SCU-Maker-Org/Mobile_Industrial_Foreign_Object_Detection_Robot/Vehicle_Code/Tracked_407/Core/Src/PID.c

//
// Created by s on 2026/9/23.
//

#include "PID.h"

/**
 * @brief 初始化PID位置控制器（带限幅参数）
 * @param[out] pid PID控制器结构体指针
 * @param[in] Kp 比例系数
 * @param[in] Ki 积分系数
 * @param[in] Kd 微分系数
 * @param[in] integral_limit 积分限幅值
 * @param[in] output_limit 输出限幅值
 */
void PID_Position_Controller_Init(PID_Position_Controller *pid,
                                  float Kp, float Ki, float Kd,
                                  float integral_limit,
                                  float output_limit) {
    pid->Kp = Kp;
    pid->Ki = Ki;
    pid->Kd = Kd;
    pid->error      = 0.0;
    pid->last_error = 0.0;
    pid->prev_error = 0.0;
    pid->differ_error = 0.0;
    pid->sum_error = 0.0;
    pid->output     = 0.0;
    pid->integral_limit = integral_limit;
    pid->output_limit   = output_limit;
}

/**
 * @brief 位置环误差累计限幅内联函数
 */
inline float Limit_Position(float cal_value, float limit_value) {
    if (cal_value > limit_value)    return limit_value;
    if (cal_value < -limit_value)   return -limit_value;

    return cal_value;
}

/**
 * @brief PID位置环更新
 * @param[out] pid PID控制器结构体指针
 * @param[in] target_val 目标值
 * @param[in] current_val 当前值
 * @return output 输出
 */
float PID_Position_Controller_Update(PID_Position_Controller *pid,
                                     float target_val,
                                     float current_val) {
    pid->error = target_val - current_val;
    pid->sum_error += pid->error;
    pid->differ_error = pid->error - pid->last_error;

    pid->output = pid->Kp * pid->error +
                  Limit_Position(pid->Ki * pid->sum_error, pid->integral_limit) +
                  pid->Kd * pid->differ_error;

    pid->last_error = pid->error;

    if (pid->output > pid->output_limit) pid->output = pid->output_limit;
    if (pid->output < -pid->output_limit) pid->output = -pid->output_limit;

    return pid->output;
}

/**
 * @brief 初始化PID速度控制器（带限幅参数）
 * @param[out] pid PID控制器结构体指针
 * @param[in] Kp 比例系数
 * @param[in] Ki 积分系数
 * @param[in] Kd 微分系数
 * @param[in] integral_limit 积分限幅值
 * @param[in] output_limit 输出限幅值
 */
void PID_Speed_Controller_Init(PID_Speed_Controller *pid,
                                  float Kp, float Ki, float Kd,
                                  float integral_limit,
                                  float output_limit) {
    pid->Kp = Kp;
    pid->Ki = Ki;
    pid->Kd = Kd;
    pid->integral   = 0.0;
    pid->error      = 0.0;
    pid->last_error = 0.0;
    pid->prev_error = 0.0;
    pid->output     = 0.0;
    pid->integral_limit = integral_limit;
    pid->output_limit   = output_limit;
}

/**
 * @brief PID速度环更新
 * @param[out] pid PID控制器结构体指针
 * @param[in] target_val 目标值
 * @param[in] current_val 当前值
 * @return output 输出
 */
float PID_Speed_Controller_Update(PID_Speed_Controller *pid,
                                  float target_val, float current_val) {
    pid->error = target_val - current_val;
    pid->integral += pid->error;
    // 积分限幅
    if (pid->integral > pid->integral_limit) pid->integral = pid->integral_limit;
    if (pid->integral < -pid->integral_limit) pid->integral = -pid->integral_limit;

    pid->output = pid->Kp * pid->error
                + pid->Ki * pid->integral
                + pid->Kd * (pid->error - pid->last_error);

    pid->last_error = pid->error;

    if (pid->output > pid->output_limit) pid->output = pid->output_limit;
    if (pid->output < -pid->output_limit) pid->output = -pid->output_limit;
    return pid->output;
}
